labodejuguete/LUDOTECNIA/hardware/PDF (DIY PCB)/neklops_GH_etch_silk_bottom.pdf

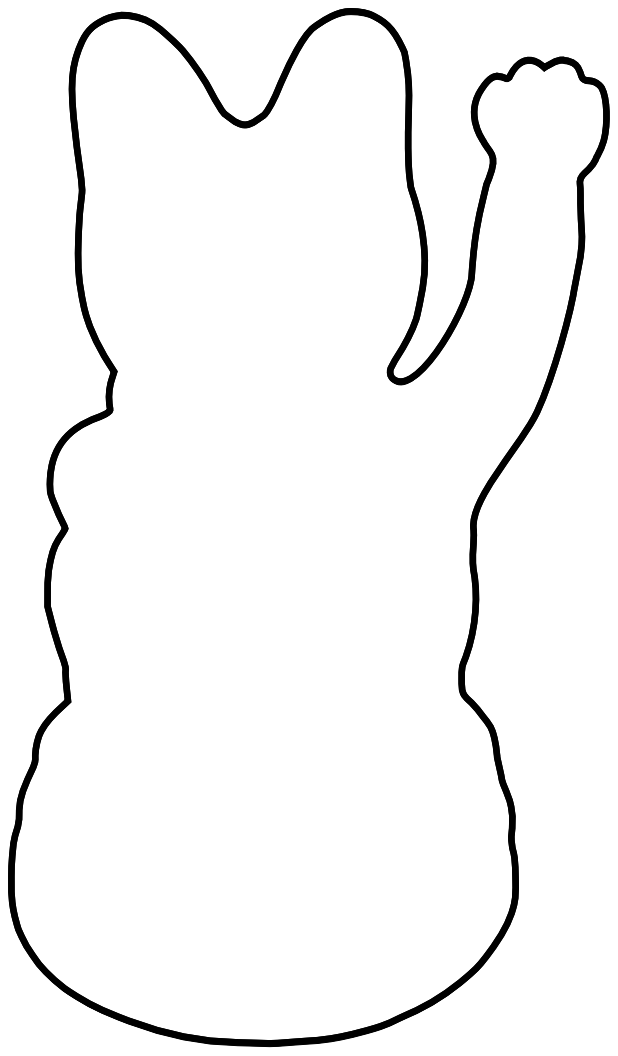
[picture p27: page 1]
