labodejuguete/LUDOTECNIA/hardware/PDF (DIY PCB)/neklops_GH_etch_silk_bottom_mirror.pdf

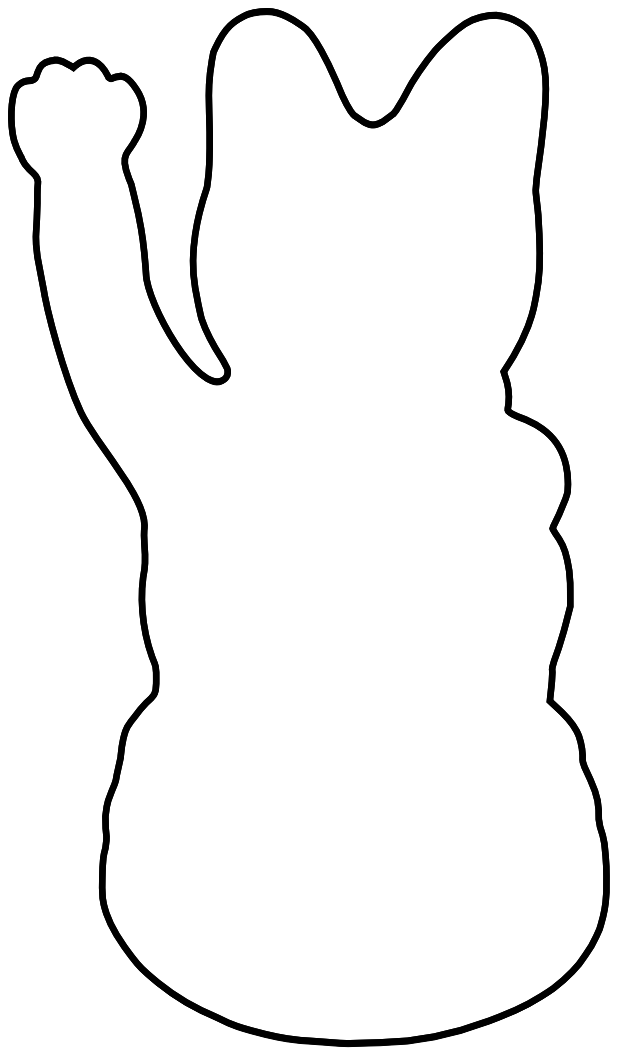
[picture p28: page 1]
