labodejuguete/LUDOTECNIA/hardware/PDF (DIY PCB)/neklops_GH_etch_silk_top.pdf

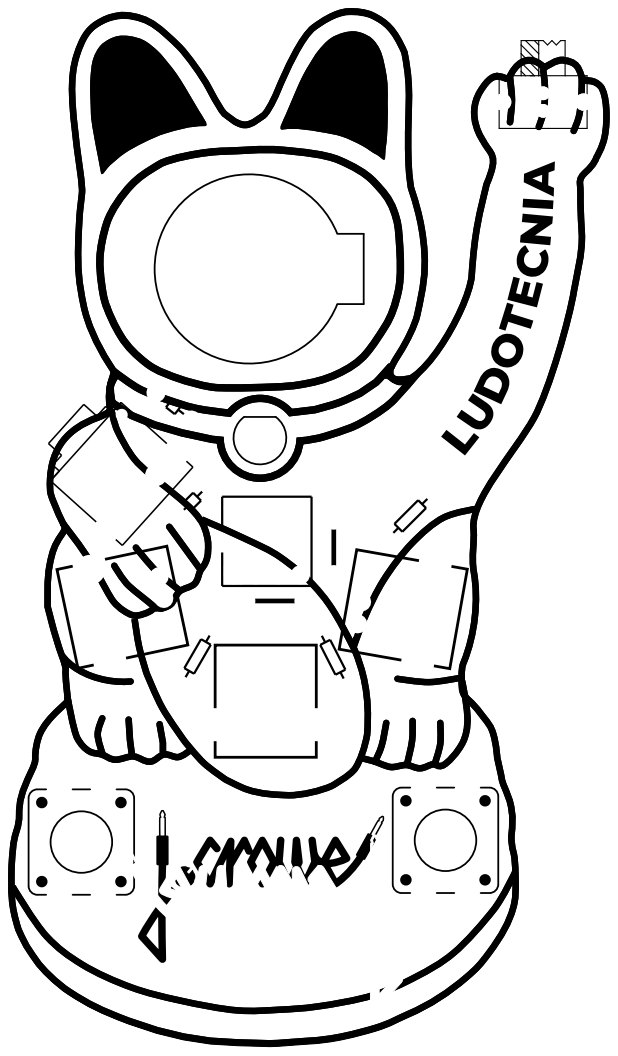
[picture p29: page 1]
