labodejuguete/LUDOTECNIA/hardware/PDF (DIY PCB)/neklops_GH_etch_silk_top_mirror.pdf

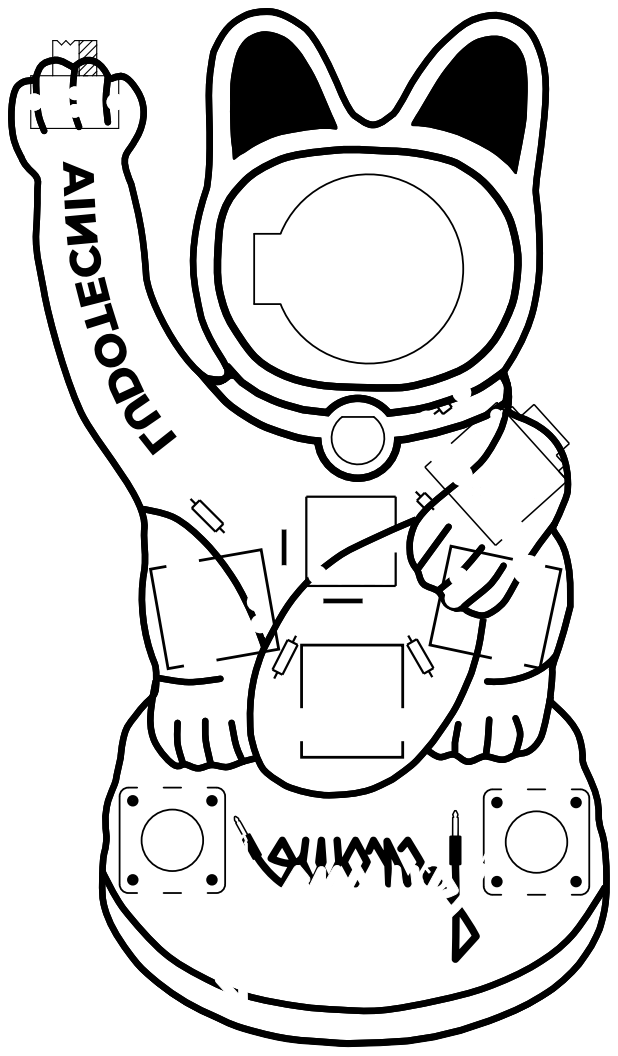
[picture p30: page 1]
